LXF-YZP/Customized_keyboard/pcb/原理图.png

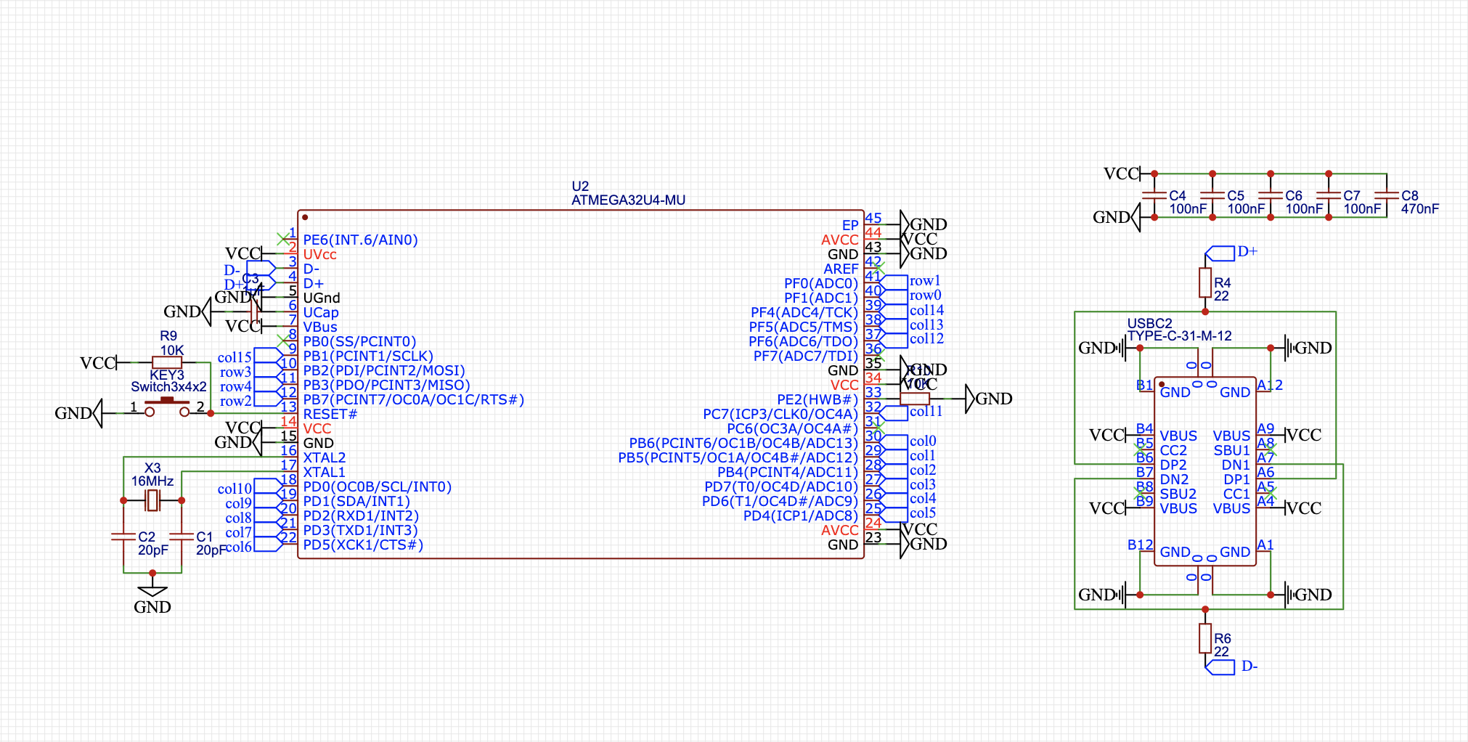
pcb/原理图.png
