LXF-YZP/Customized_keyboard/photo/5ADB421E83C6A2962B34C76C5DCE094A.png

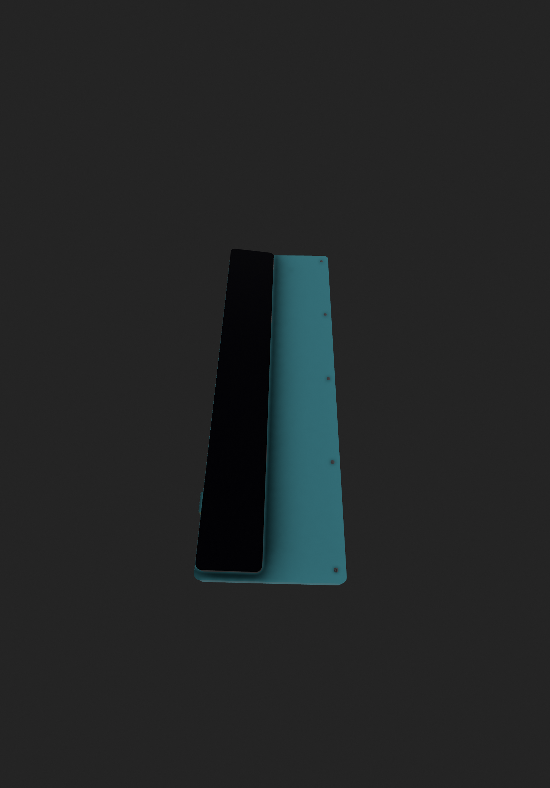
photo/5ADB421E83C6A2962B34C76C5DCE094A.png
