LXF-YZP/Customized_keyboard/photo/15C5CD941F69A8B925AC5FE7A346DBD2.png

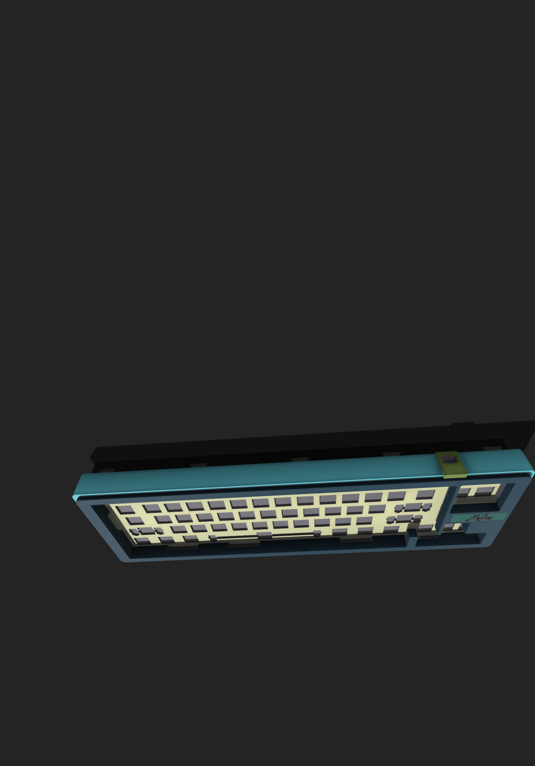
photo/15C5CD941F69A8B925AC5FE7A346DBD2.png
