LXF-YZP/Customized_keyboard/photo/68vim.png

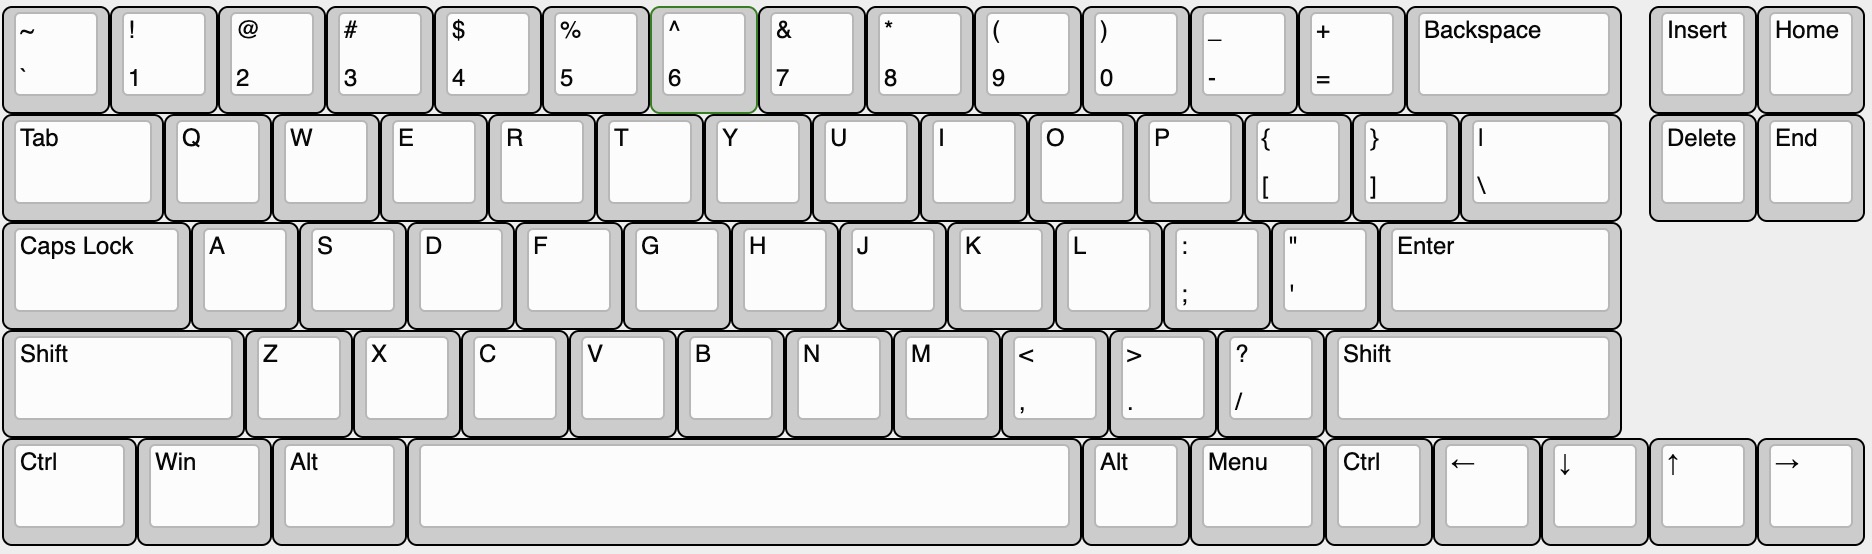
photo/68vim.png
