LXF-YZP/Customized_keyboard/photo/79.png

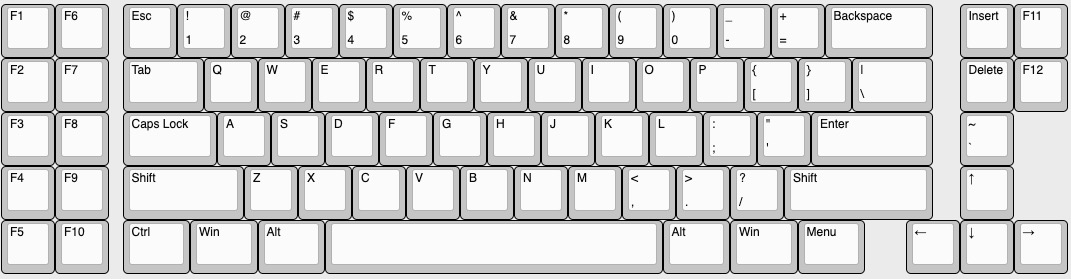
photo/79.png
