LXF-YZP/Customized_keyboard/photo/91DCE8556651DD74BBD1BB2E9E0A88F6.png

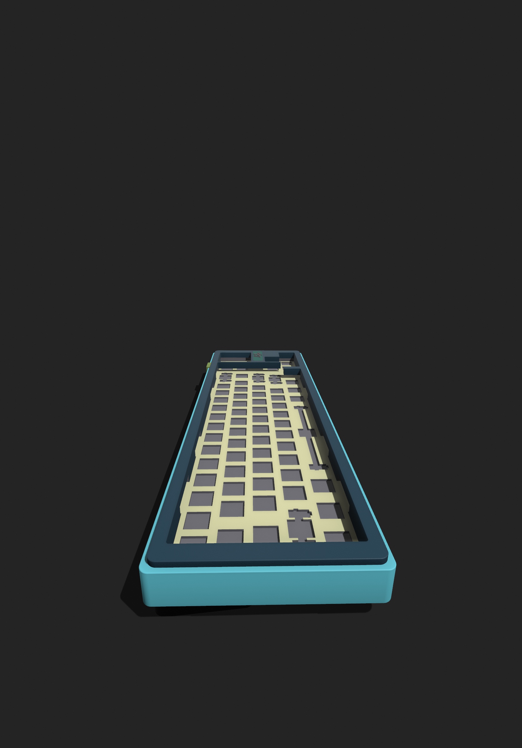
photo/91DCE8556651DD74BBD1BB2E9E0A88F6.png
