LXF-YZP/Customized_keyboard/photo/D7EFD2467501DA16BB903C50A47A5C07.png

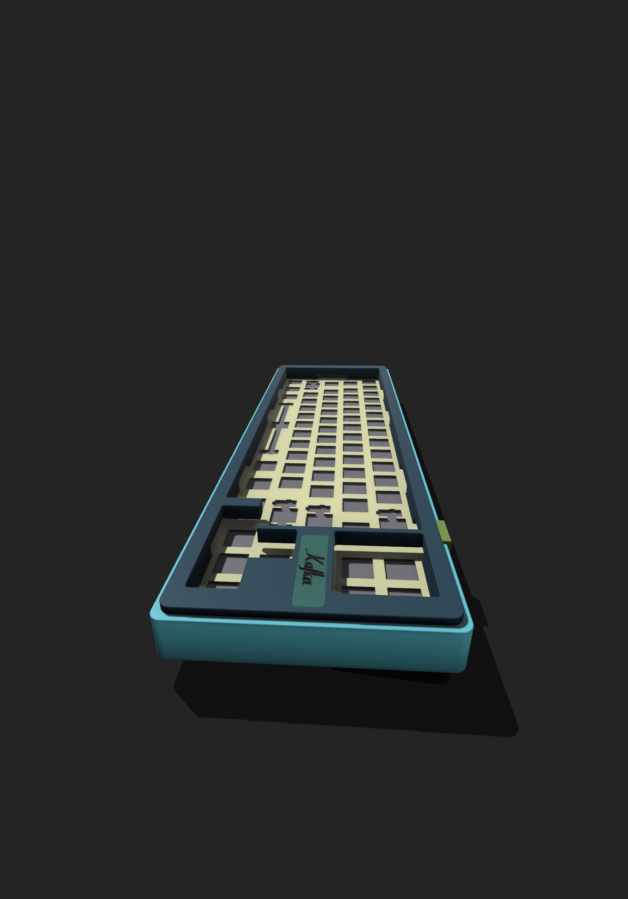
photo/D7EFD2467501DA16BB903C50A47A5C07.png
