LXF-YZP/Customized_keyboard/photo/EC3D5700C9C32B06DA7DAF4B408FBE42.png

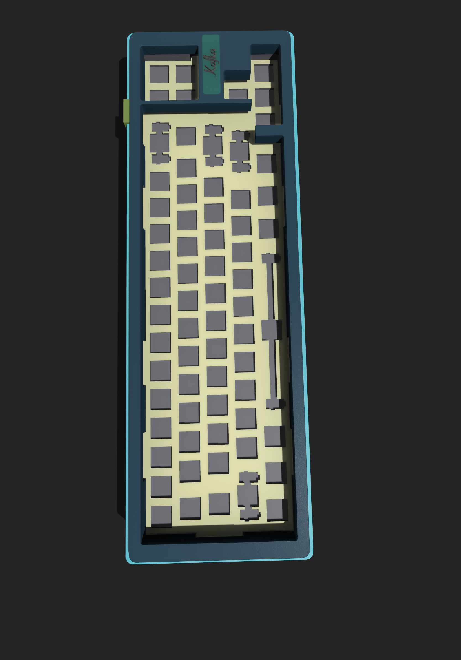
photo/EC3D5700C9C32B06DA7DAF4B408FBE42.png
