LXF-YZP/Customized_keyboard/photo/F4DC30CC0DEFC94D06A29A3ABAEBBCF9.png

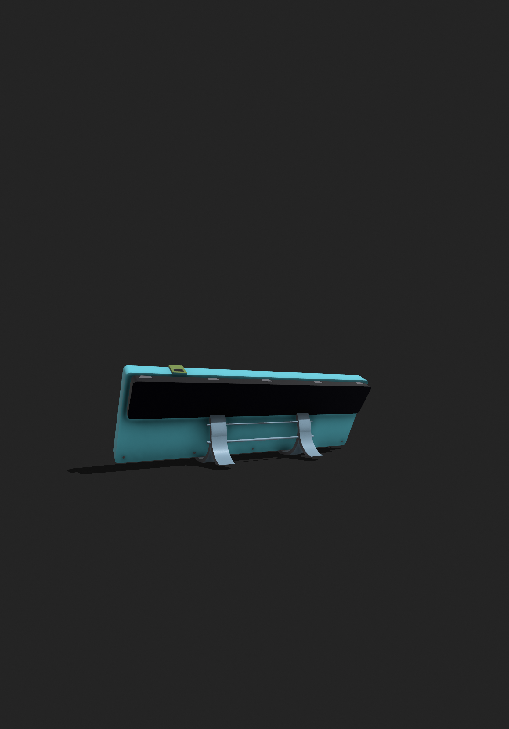
photo/F4DC30CC0DEFC94D06A29A3ABAEBBCF9.png
