LXF-YZP/Customized_keyboard/screw/5852D7CC401917460D92E522B1FBCC75.png

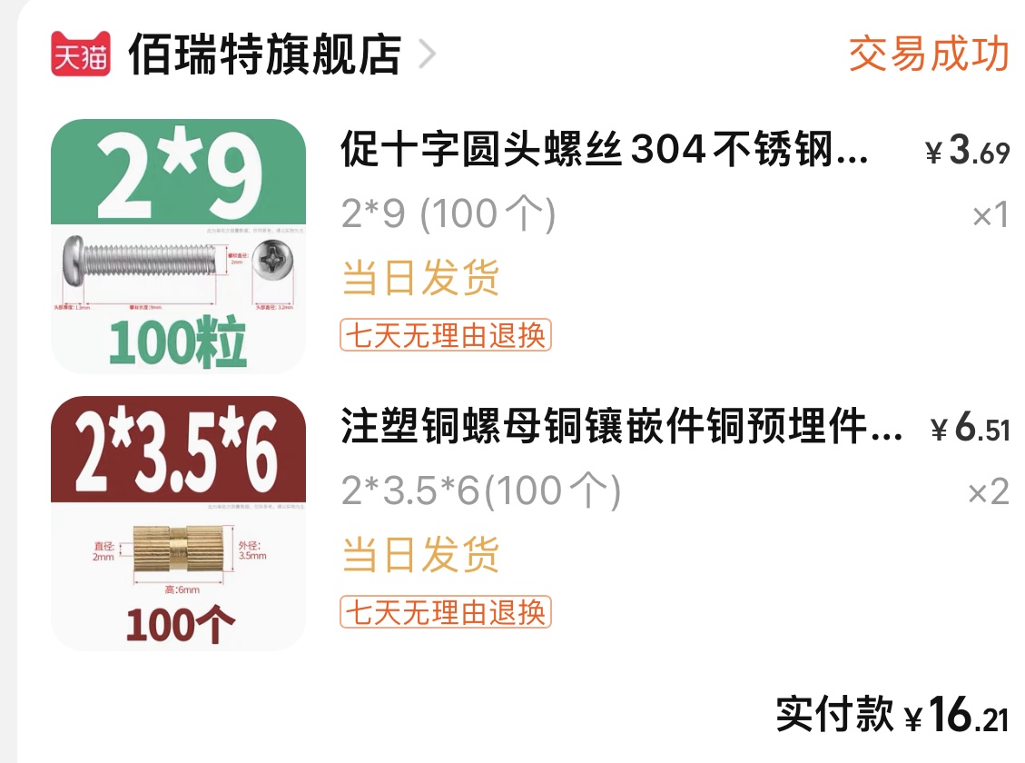
screw/5852D7CC401917460D92E522B1FBCC75.png
