LXF-YZP/Customized_keyboard/photo/9C022CC21A434EFF853F7C600D4C19E0.png

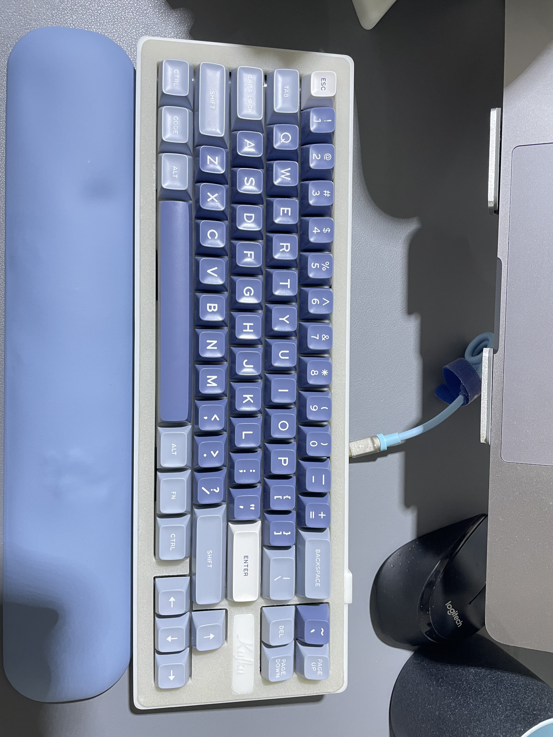
photo/9C022CC21A434EFF853F7C600D4C19E0.png
