LXF-YZP/Customized_keyboard/photo/425D978D7A2E98BD8BDB00565A1A10D3.png

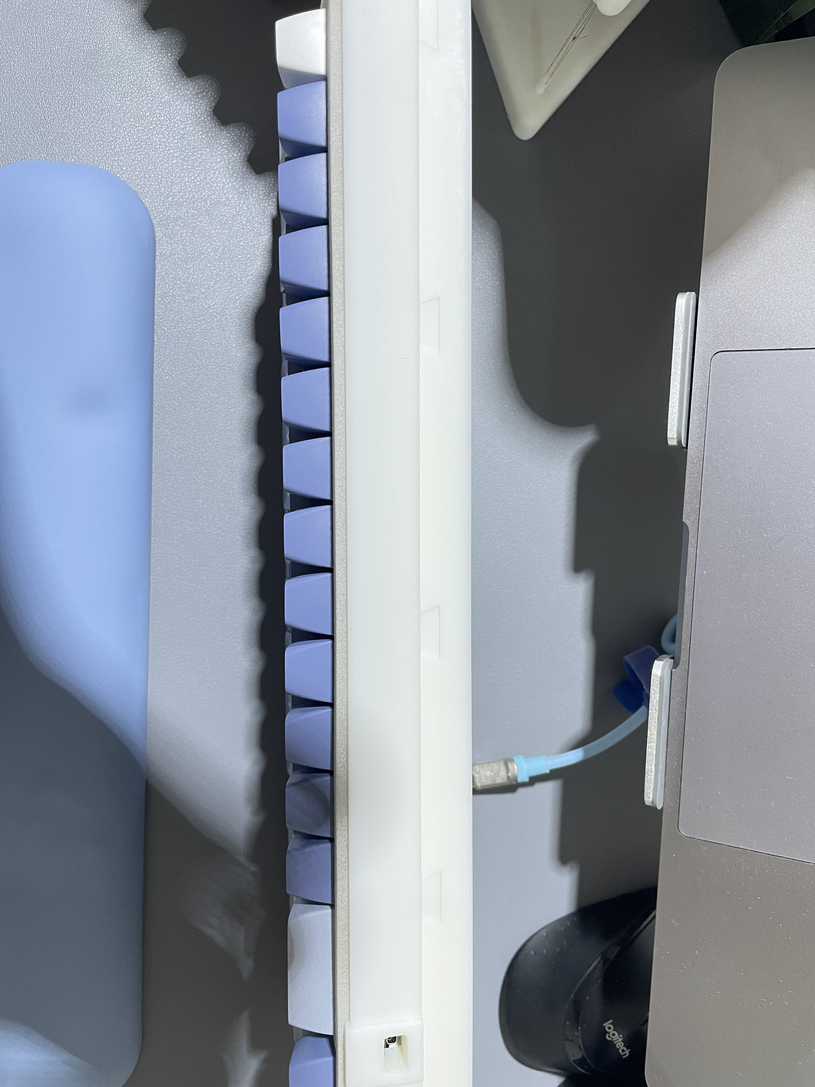
photo/425D978D7A2E98BD8BDB00565A1A10D3.png
